robcmills/karn-keyboard/images/karn-right-pcb.png

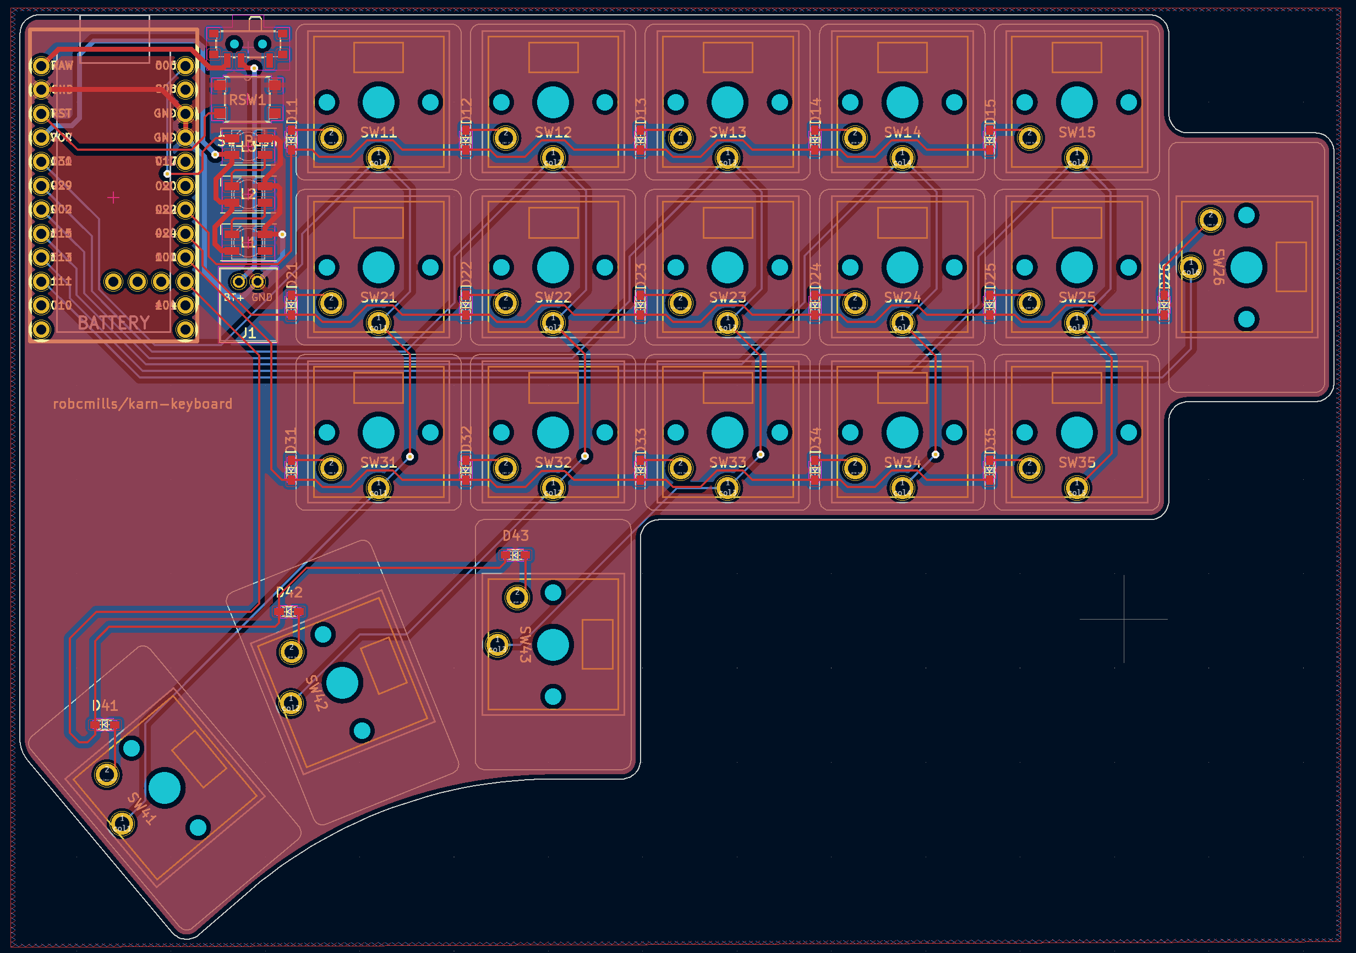
images/karn-right-pcb.png
