robcmills/karn-keyboard/images/karn-right-top.jpg

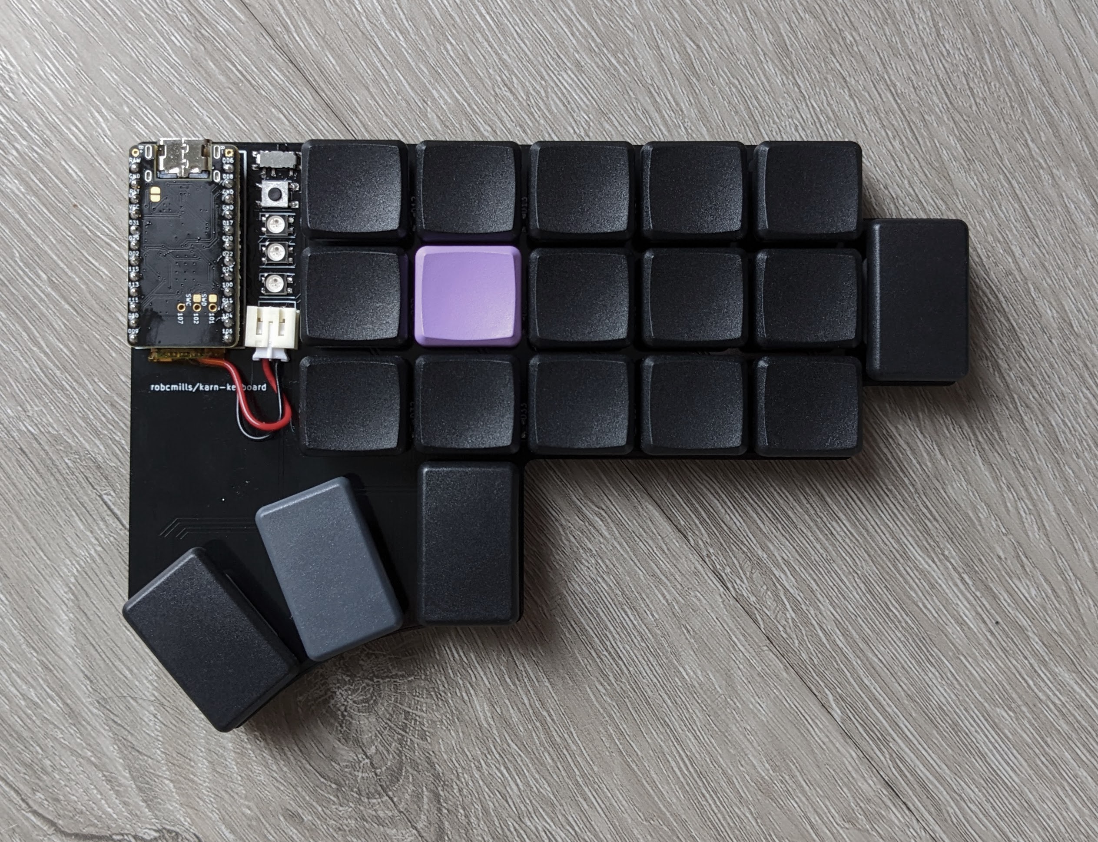
images/karn-right-top.jpg
