robcmills/karn-keyboard/images/nec-personal-word-processor-100.jpg

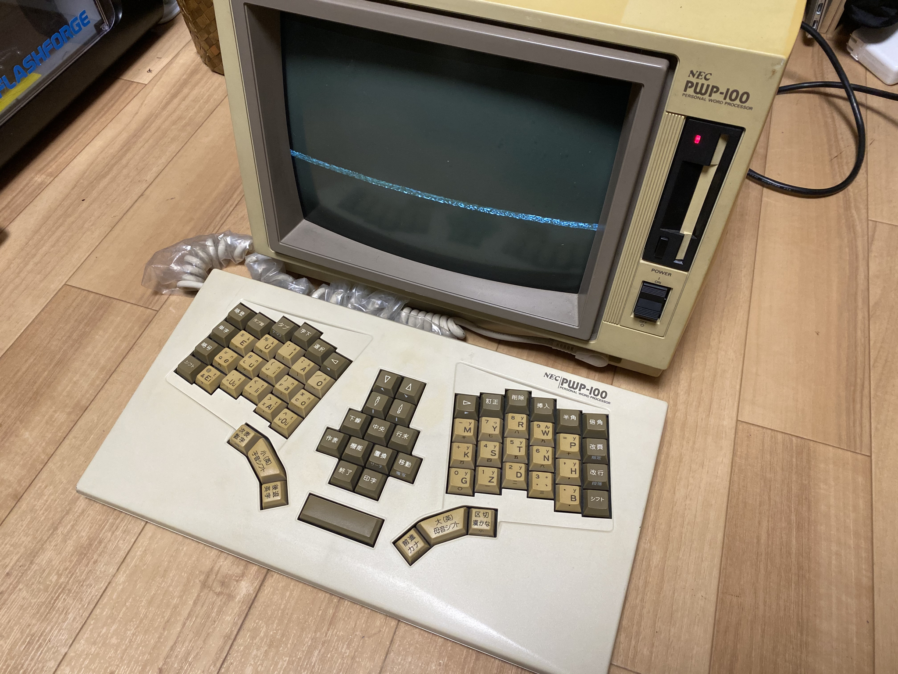
images/nec-personal-word-processor-100.jpg
